maarten-pennings/ElektroClub2022/pcboutline/view-3b.jpg

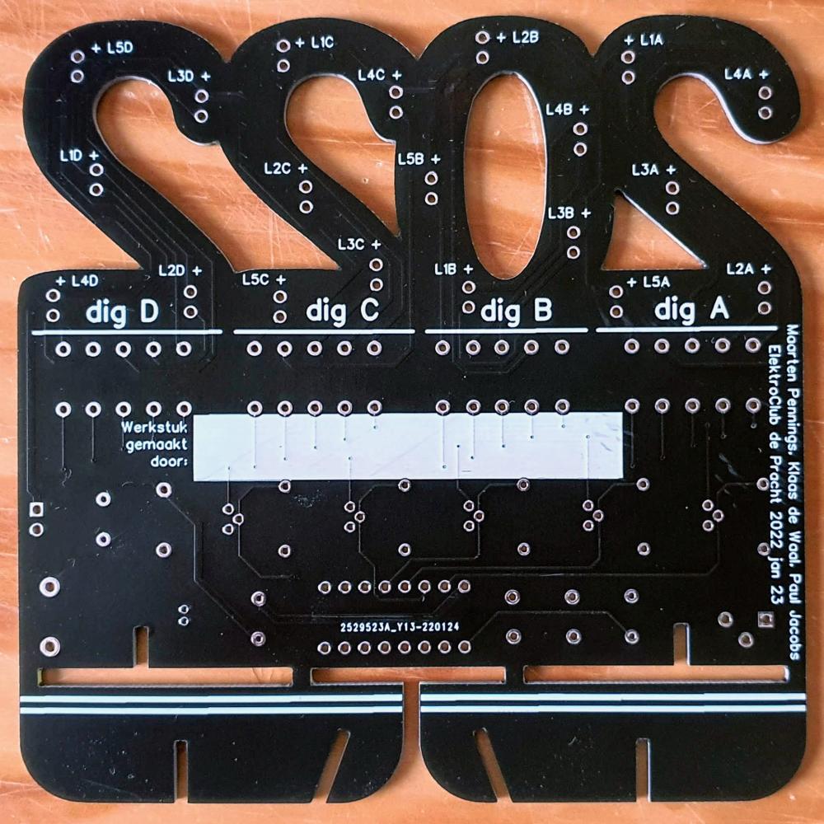
pcboutline/view-3b.jpg
